Dakkaron/Fairberry/Images/black_standing.jpg

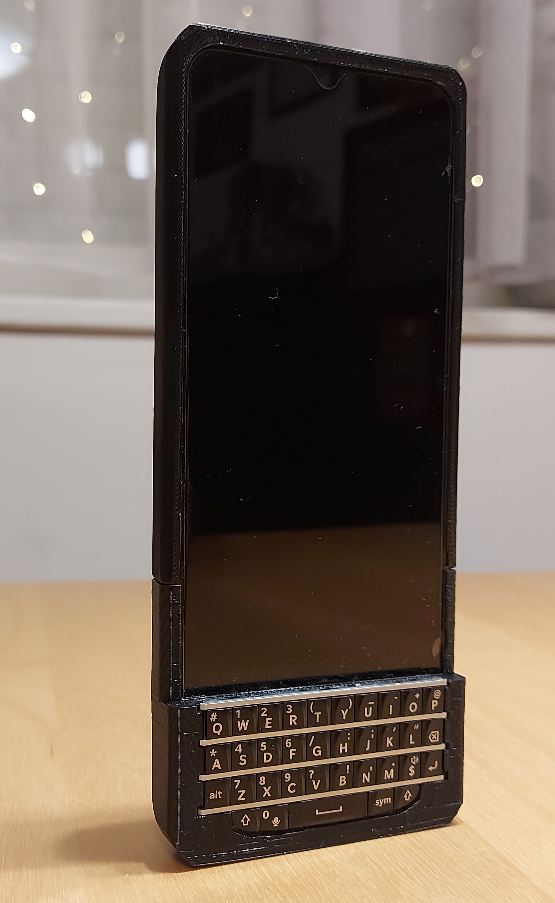
Images/black_standing.jpg
