Dakkaron/Fairberry/Images/copper_wood.jpg

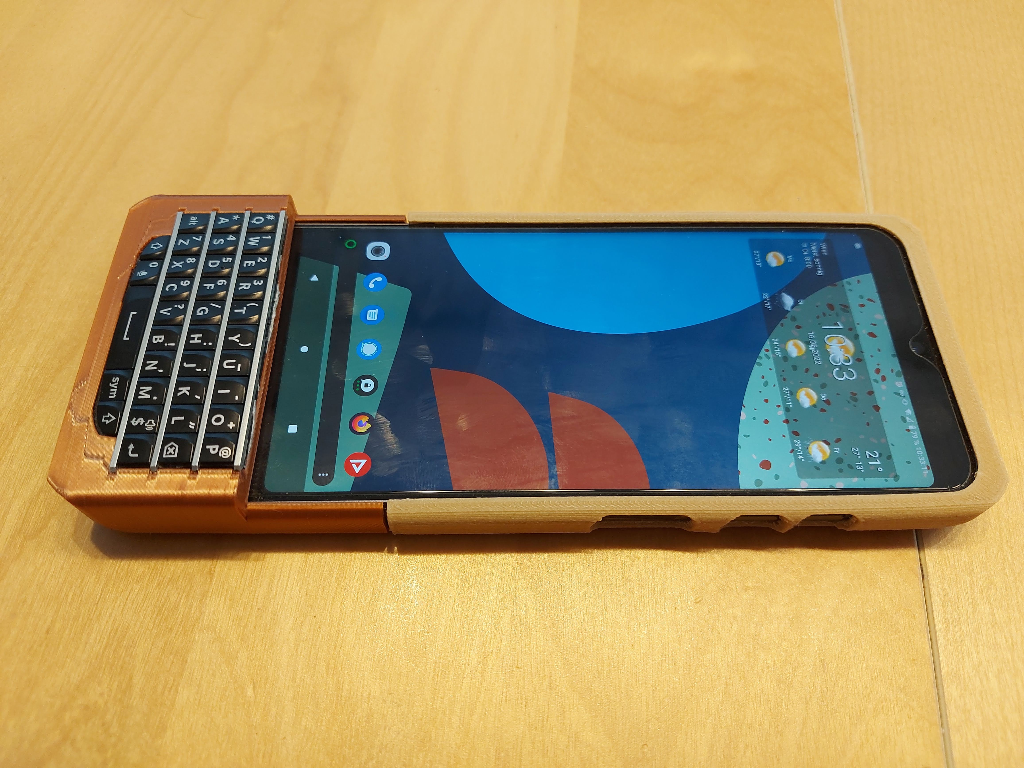
Images/copper_wood.jpg
