Dakkaron/Fairberry/Images/keyboard_attached_underside.jpeg

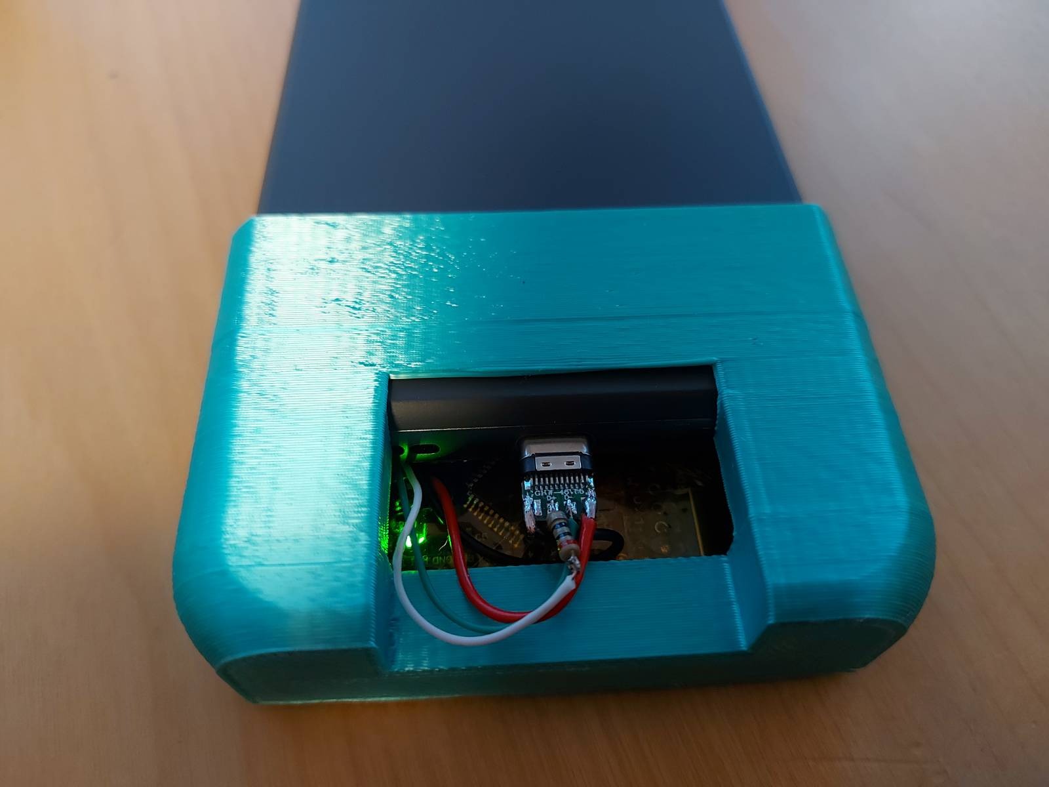
Images/keyboard_attached_underside.jpeg
