Dakkaron/Fairberry/Images/keyboard_detached_top.jpeg

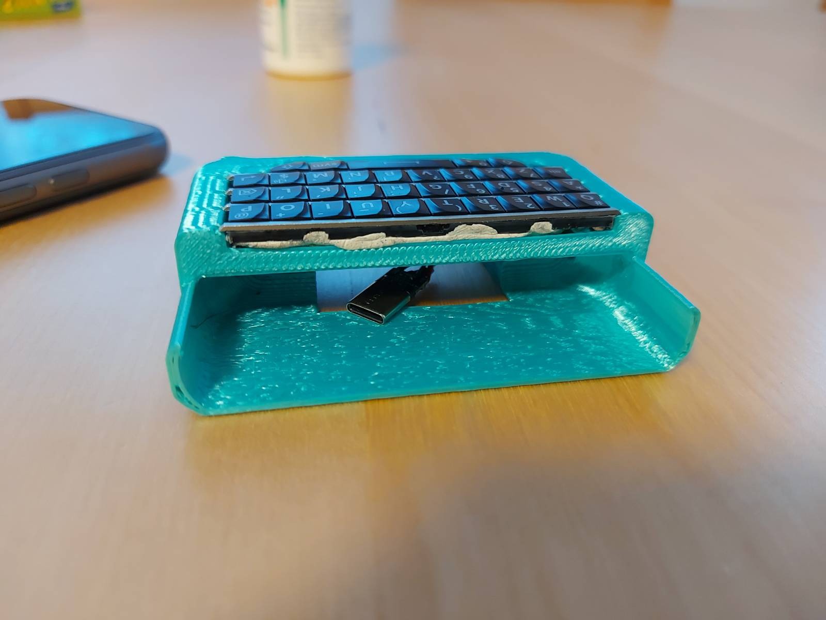
Images/keyboard_detached_top.jpeg
