Dakkaron/Fairberry/Images/USB_Connection.png

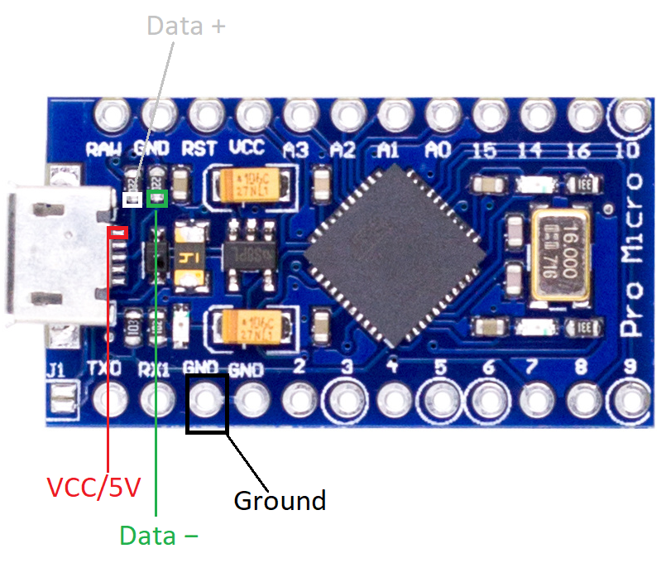
Images/USB_Connection.png
