Dakkaron/Fairberry/BBQ10/constants.h

#define K_SYM_COL 0
#define K_SYM_ROW 2
#define K_SYM K_SYM_COL, K_SYM_ROW

#define K_MIC_COL 0
#define K_MIC_ROW 6
#define K_MIC K_MIC_COL, K_MIC_ROW

#define K_LSH_COL 1
#define K_LSH_ROW 6
#define K_LSH K_LSH_COL, K_LSH_ROW

#define K_RSH_COL 2
#define K_RSH_ROW 3
#define K_RSH K_RSH_COL, K_RSH_ROW

#define K_ENTER_COL 3
#define K_ENTER_ROW 3
#define K_ENTER K_ENTER_COL, K_ENTER_ROW

#define K_ALT_COL 0
#define K_ALT_ROW 4
#define K_ALT K_ALT_COL, K_ALT_ROW

#define KEY_PRESSED true
#define KEY_RELEASED false
